houseofthe051010/ESP32-ESPNOW-Walkie-Talkie/CUSTOM PCB FABRICATION/SOURCE KICAD/.easyeda_cache/617b05f9bba7410b96c001093d8189e4.step

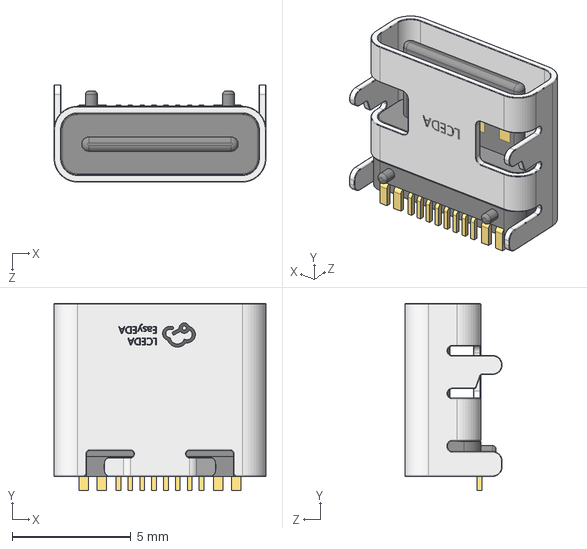
[picture p26: CAD file, 2026-07-25]
CUSTOM PCB FABRICATION/SOURCE KICAD/.easyeda_cache/617b05f9bba7410b96c001093d8189e4.step
8.94 x 7.90 x 4.10 mm
