houseofthe051010/ESP32-ESPNOW-Walkie-Talkie/SOURCE CAD/INDIVIDUAL STLS/walkie_talkie_top_cover.stl

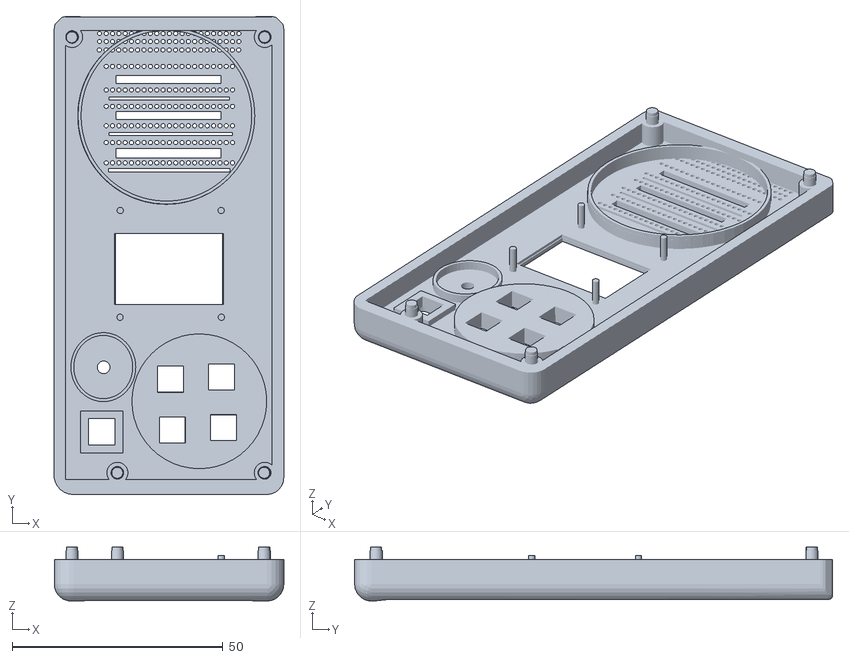
[picture p27: CAD file, 2026-06-11]
SOURCE CAD/INDIVIDUAL STLS/walkie_talkie_top_cover.stl
54.5 x 113.5 x 12.8
