houseofthe051010/ESP32-ESPNOW-Walkie-Talkie/CUSTOM PCB FABRICATION/SOURCE KICAD/.easyeda_cache/10d570588d4c4ccca30b4bf25476f535.step

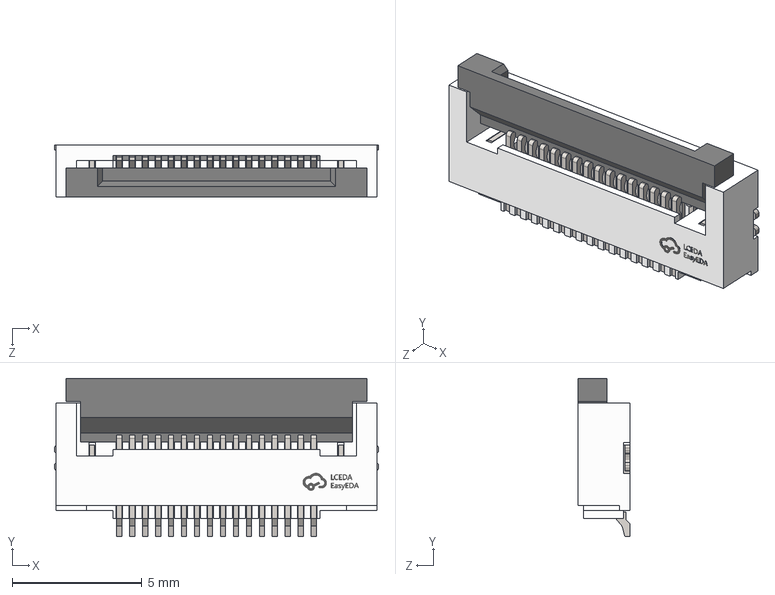
[picture p28: CAD file, 2026-07-25]
CUSTOM PCB FABRICATION/SOURCE KICAD/.easyeda_cache/10d570588d4c4ccca30b4bf25476f535.step
12.5 x 6.10 x 2.01 mm
