houseofthe051010/ESP32-ESPNOW-Walkie-Talkie/CUSTOM PCB FABRICATION/SOURCE KICAD/.easyeda_cache/ea3d09bd0a8e416194da70a34a37168f.step

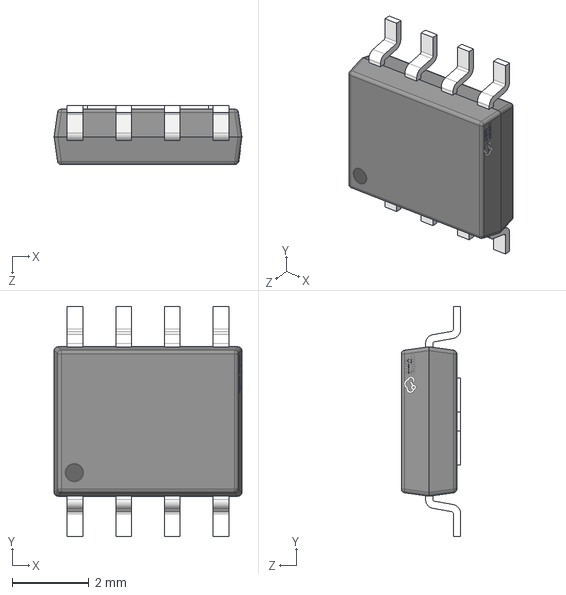
[picture p29: CAD file, 2026-07-25]
CUSTOM PCB FABRICATION/SOURCE KICAD/.easyeda_cache/ea3d09bd0a8e416194da70a34a37168f.step
4.90 x 6.00 x 1.55 mm
