houseofthe051010/ESP32-ESPNOW-Walkie-Talkie/CUSTOM PCB FABRICATION/SOURCE KICAD/.easyeda_cache/edc2f28e721b49ee8c25b04b981b88c3.step

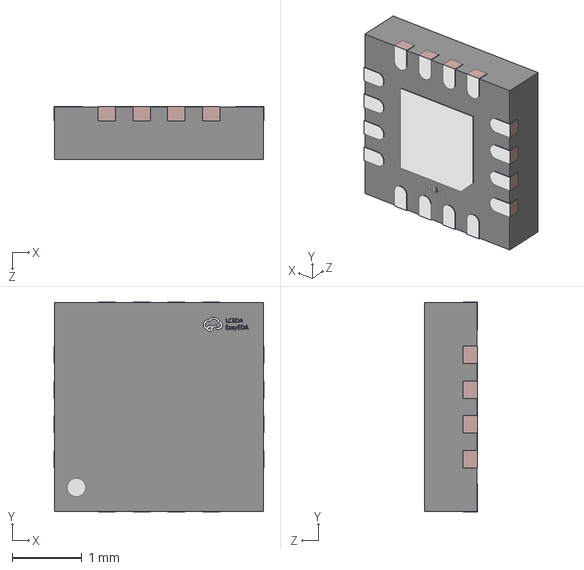
[picture p30: CAD file, 2026-07-25]
CUSTOM PCB FABRICATION/SOURCE KICAD/.easyeda_cache/edc2f28e721b49ee8c25b04b981b88c3.step
3.02 x 3.02 x 0.761 mm
