houseofthe051010/ESP32-ESPNOW-Walkie-Talkie/CUSTOM PCB FABRICATION/SOURCE KICAD/.easyeda_cache/2e35dca8e7854ed683469f8d54d1ef17.step

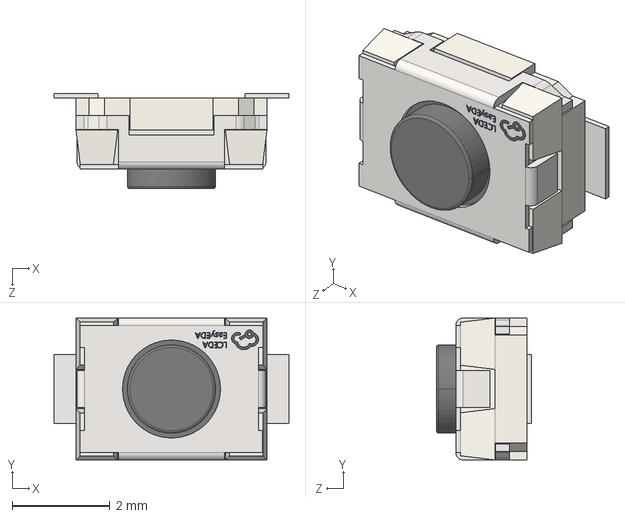
[picture p31: CAD file, 2026-07-25]
CUSTOM PCB FABRICATION/SOURCE KICAD/.easyeda_cache/2e35dca8e7854ed683469f8d54d1ef17.step
4.80 x 2.90 x 1.95 mm
